RubberyFun/endless-orgasm-machine/doc/building/exhaust_sensor.png

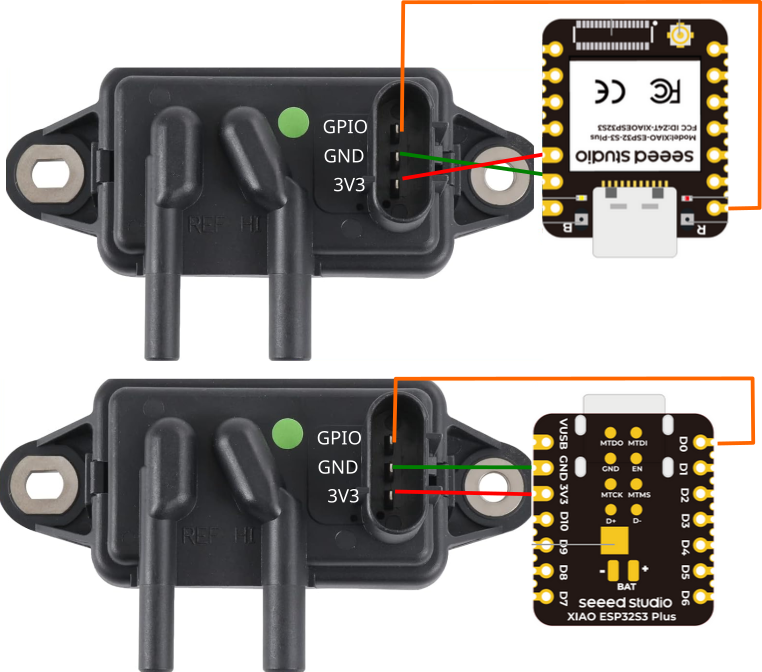
doc/building/exhaust_sensor.png
