RubberyFun/endless-orgasm-machine/doc/building/mprl sensor.png

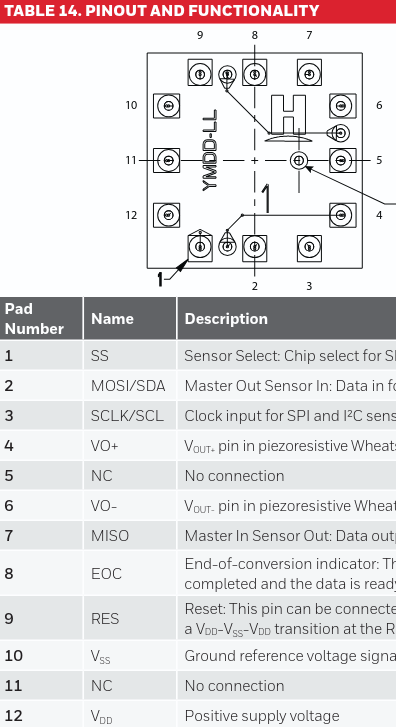
doc/building/mprl sensor.png
