RubberyFun/endless-orgasm-machine/doc/building/mpxv_sensor.png

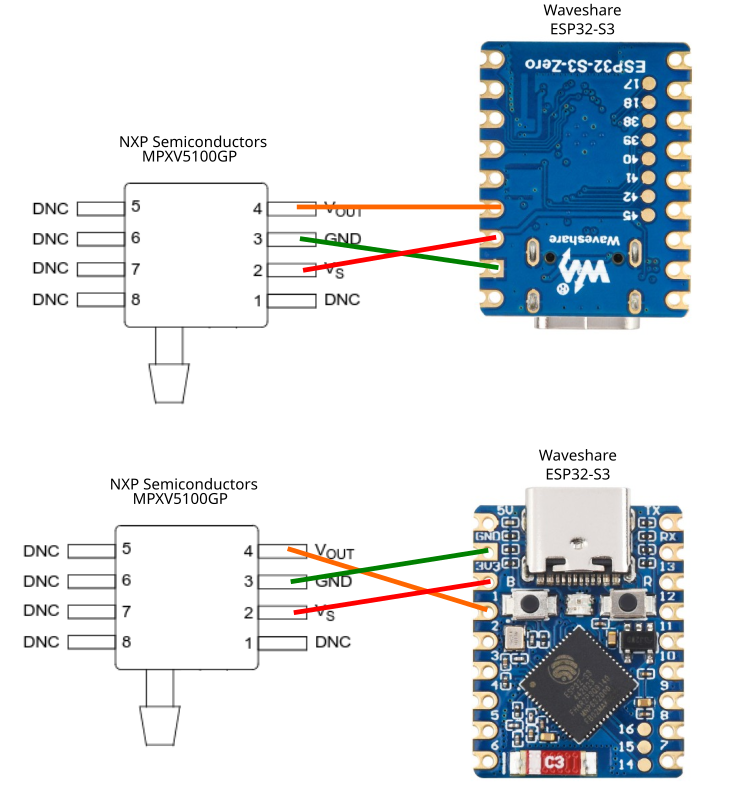
doc/building/mpxv_sensor.png
