RubberyFun/endless-orgasm-machine/doc/building/seed_wiring.png

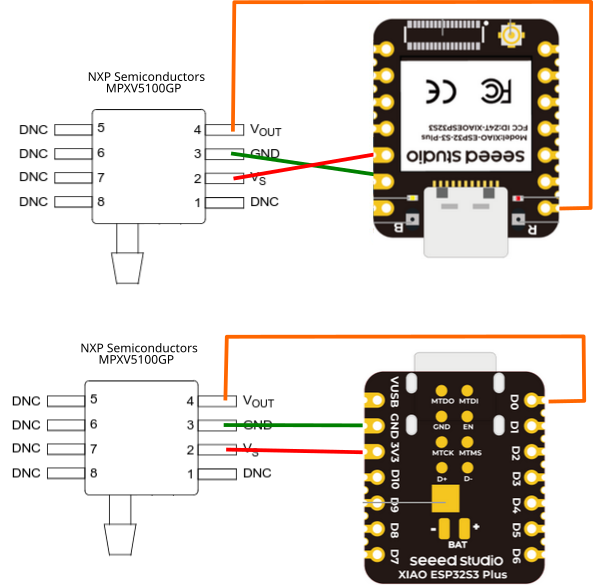
doc/building/seed_wiring.png
