RubberyFun/endless-orgasm-machine/doc/building/Simple analog sensor.png

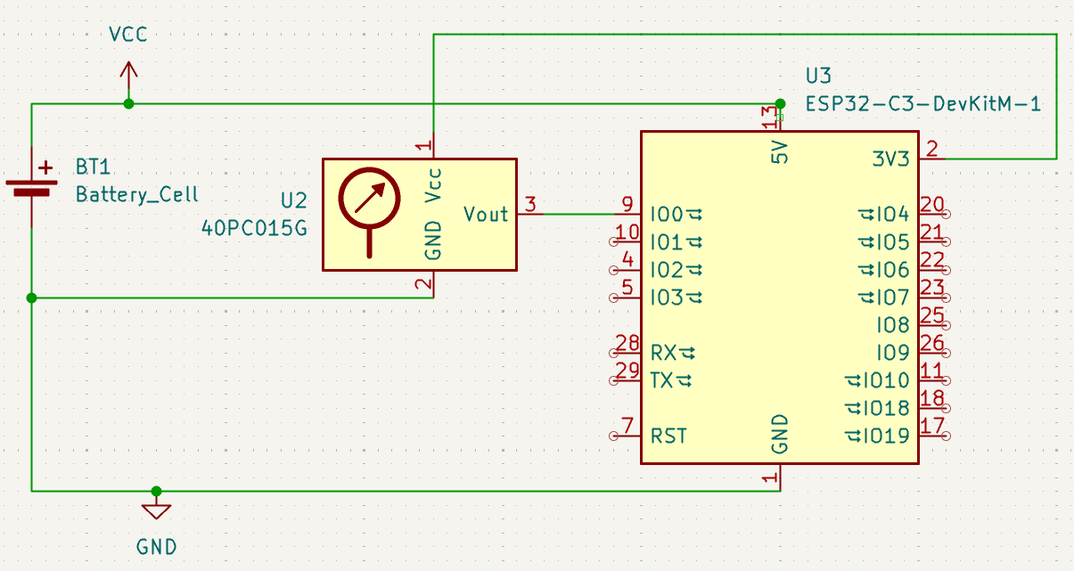
doc/building/Simple analog sensor.png
