RubberyFun/endless-orgasm-machine/src/config_defs.c

#include "config_defs.h"
#include "api/broadcast.h"
#include "config.h"
#include "eom-hal-esp32.h"
#include "esp_err.h"
#include "esp_log.h"
#include "nvs.h"
#include "polyfill.h"
#include <freertos/FreeRTOS.h>
#include <freertos/semphr.h>
#include <stddef.h>
#include <stdio.h>
#include <string.h>
#include <sys/stat.h>
#include <unistd.h>

#define MAX_FILE_PATH_LEN 120

#define NVS_NAMESPACE "config"
#define NVS_LAST_CONFIG_FILE "_filename"

static const char* TAG = "config_defs";

static StaticSemaphore_t sFileMutexStatic;
static SemaphoreHandle_t sFileMutex = NULL;

extern CONFIG_DEFS;

static esp_err_t _store_last_filename(void) {
    esp_err_t err;
    nvs_handle_t nvs;

    err = nvs_open(NVS_NAMESPACE, NVS_READWRITE, &nvs);
    if (err != ESP_OK) goto cleanup;

    err = nvs_set_str(nvs, NVS_LAST_CONFIG_FILE, Config._filename);
    if (err != ESP_OK) goto cleanup;

    err = nvs_commit(nvs);
    if (err != ESP_OK) goto cleanup;

    ESP_LOGI(TAG, "Set last opened filename to: %s\n", Config._filename);
    nvs_close(nvs);
    return ESP_OK;

cleanup:
    ESP_LOGW(TAG, "Trouble storing current config filename: %s\n", esp_err_to_name(err));
    if (nvs) nvs_close(nvs);
    return err;
}

esp_err_t config_init(void) {
    esp_err_t err;
    nvs_handle_t nvs;

    ESP_LOGI(TAG, "Initializing Config access.");

    // Initialize semaphore
    sFileMutex = xSemaphoreCreateMutexStatic(&sFileMutexStatic);

    err = nvs_open(NVS_NAMESPACE, NVS_READONLY, &nvs);
    if (err != ESP_OK) goto defaults;

    size_t len = CONFIG_PATH_MAX;
    err = nvs_get_str(nvs, NVS_LAST_CONFIG_FILE, Config._filename, &len);
    if (err != ESP_OK) goto defaults;

    err = config_load_from_sd(Config._filename, &Config);
    if (err != ESP_OK) goto defaults;

    ESP_LOGI(TAG, "Config loaded from SD: %s\n", Config._filename);

    nvs_close(nvs);

    ESP_LOGI(TAG, "Config initialization complete.");
    return ESP_OK;

defaults:
    if (nvs) nvs_close(nvs);

    if (err == ESP_ERR_NVS_NOT_FOUND || err == ESP_ERR_NOT_FOUND) {
        char path[CONFIG_PATH_MAX + 1] = { 0 };

        //SDHelper_getAbsolutePath(path, CONFIG_PATH_MAX, CONFIG_FILENAME);
        err = config_load_from_sd(CONFIG_FILENAME, &Config);
    }

    if (err != ESP_OK) {
        ESP_LOGW(
            TAG,
            "Trouble loading previous config file, falling back to default: %s\n",
            esp_err_to_name(err)
        );

        config_load_default(&Config);

        if (err == ESP_ERR_INVALID_ARG) {
            //ui_toast("%s", _("Configuration file corrupt. Default values will be used."));
        } else {
            //ui_toast("%s", _("Configuration not found. Default values will be used."));
        }
    }

    return err;
}

// get_config_to_string
void config_serialize(config_t* cfg, char* buf, size_t buflen) {
    cJSON* root = cJSON_CreateObject();
    config_to_json(root, cfg);
    cJSON_PrintPreallocated(root, buf, buflen, true);
    cJSON_Delete(root);
}

// set_config_from_string
esp_err_t config_deserialize(config_t* cfg, const char* buf) {
    esp_err_t err = ESP_OK;
    cJSON* root = cJSON_Parse(buf);
    if (root == NULL) err = ESP_ERR_INVALID_ARG;
    json_to_config(root, cfg);
    cJSON_Delete(root);
    return err;
}

// get_config_to_json
void config_to_json(cJSON* root, config_t* cfg) {
    _config_defs(CFG_GET, root, cfg, NULL, NULL, NULL, 0, NULL);

    // Add version information:
    //cJSON_AddNumberToObject(root, "$version", cfg->_version ? cfg->_version :0);
}

static void _validate_config(config_t* cfg) {
    // Bluetooth and WiFi cannot operate at the same time.
    if (cfg->wifi_on && cfg->bt_on && !cfg->force_bt_coex) {
        ESP_LOGW(TAG, "Not enough memory for WiFi and Bluetooth, disabling BT.");
        cfg->bt_on = false;
    }

    // Update hardware:
    eom_hal_set_sensor_sensitivity(cfg->sensor_sensitivity);
}

static void _migrate_config(cJSON* root) {
    migration_result_t ret = config_system_migrate(root);
    ESP_LOGI(TAG, "Config migrated with status: %d", ret);

    switch (ret) {
    case MIGRATION_COMPLETE:
        config_enqueue_save(1);
        //ui_toast("%s", _("Your config file has updated to work with this version."));
        return;

    case MIGRATION_ERR_TOO_NEW:
        // ui_toast(
        //     "%s",
        //     _("Your config file was created with a newer firmware version and cannot be used.")
        // );
        break;

    case MIGRATION_ERR_BAD_DATA:
        // ui_toast(
        //     "%s", _("There was an error updating your config file to work with this version.")
        // );
        //);
        break;

    default: return;
    }
}

// set_config_from_json
void json_to_config(cJSON* root, config_t* cfg) {
    _migrate_config(root);
    _config_defs(CFG_SET, root, cfg, NULL, NULL, NULL, 0, NULL);
    _validate_config(cfg);

    cJSON* root_version = cJSON_GetObjectItem(root, "$version");
    if (root_version != NULL) cfg->_version = root_version->valueint;
}

// merge_config_from_json
void json_to_config_merge(cJSON* root, config_t* cfg) {
    _migrate_config(root);
    _config_defs(CFG_MERGE, root, cfg, NULL, NULL, NULL, 0, NULL);
    _validate_config(cfg);
}

bool set_config_value(const char* option, const char* value, bool* require_reboot) {
    if (_config_defs(CFG_SET, NULL, &Config, option, value, NULL, 0, require_reboot)) {
        _validate_config(&Config);
        return true;
    }

    return false;
}

bool get_config_value(const char* option, char* buffer, size_t len) {
    if (_config_defs(CFG_GET, NULL, &Config, option, NULL, buffer, len, NULL)) {
        return true;
    }

    return false;
}

/**
 * @brief Enqueue a save after a particular delay. To check or tick, pass -1 for arg.
 *
 * @param delay Delay in MS after which to save, to prevent repeated duplicates. 0 to save now, -1
 * to tick.
 */
void config_enqueue_save(long delay) {
    static unsigned long save_at_ms_tick = 0;
    unsigned long millis = esp_timer_get_time() / 1000UL;

    if (delay > 0) {
        // Queue a future save:
        save_at_ms_tick = millis + delay;
    } else {
        if (delay == 0 || (save_at_ms_tick > 0 && save_at_ms_tick < millis)) {
            if (Config._filename[0] == '\0') {
                ESP_LOGW(TAG, "Attempt to save config without a _filename!");
                save_at_ms_tick = 0;
                return;
            }

            ESP_LOGI(
                TAG,
                "Saving now from future save queue... (delay=%ld, at=%ld, ms=%ld)",
                delay,
                save_at_ms_tick,
                millis
            );

            config_save_to_sd(Config._filename, &Config);
            api_broadcast_config();
            save_at_ms_tick = 0;
        }
    }
}

/**
 * Cast a string to a bool. Accepts "false", "no", "off", "0" to false, all other
 * strings cast to true.
 * @param a
 * @return
 */
bool atob(const char* a) {
    return !(
        strcasecmp(a, "false") == 0 || strcasecmp(a, "no") == 0 || strcasecmp(a, "off") == 0 ||
        strcasecmp(a, "0") == 0
    );
}

// Here There Be Dragons Indeed

esp_err_t config_load_from_sd(const char* path, config_t* cfg) {
    esp_err_t err = ESP_OK;
    FILE* f = NULL;
    long fsize;
    char* buffer = NULL;
    size_t result;

    if (!xSemaphoreTake(sFileMutex, portMAX_DELAY)) {
        ESP_LOGW(TAG, "Failed to take file lock for config load.");
        err = ESP_ERR_TIMEOUT;
        goto cleanup;
    }

    f = fopen(path, "r");

    // Sometimes the first file read fails:
    if (!f) {
        f = fopen(path, "r");
    }

    if (!f) {
        ESP_LOGW(TAG, "File does not exist: %s", path);
        err = ESP_ERR_NOT_FOUND;
        goto cleanup;
    }

    if (f == NULL) {
        ESP_LOGE(TAG, "Failed to open file for reading: %s", path);
        err = ESP_FAIL;
        goto cleanup;
    }

    fseek(f, 0, SEEK_END);
    fsize = ftell(f);
    rewind(f);

    ESP_LOGD(TAG, "Allocating %ld bytes for file: %s", fsize, path);
    buffer = (char*)malloc(fsize + 1);

    if (!buffer) {
        ESP_LOGE(TAG, "Failed to allocate memory for file: %s", path);
        err = ESP_FAIL;
        goto cleanup;
    }

    result = fread(buffer, 1, fsize, f);
    buffer[fsize] = '\0';

    if (result != fsize) {
        ESP_LOGE(TAG, "Failed to read file: %s", path);
        err = ESP_FAIL;
        goto cleanup;
    }

    ESP_LOGI(TAG, "Loaded %ld bytes from %s\n%s", fsize, path, buffer);

    err = config_deserialize(cfg, buffer);
    if (err != ESP_OK) {
        ESP_LOGE(TAG, "Error deserializing config file.");
        goto cleanup;
    }

    // Update config path:
    strlcpy(cfg->_filename, path, CONFIG_PATH_MAX);

    if (&Config == cfg) {
        _store_last_filename();
    }

cleanup:
    if (f) fclose(f);
    if (buffer) free(buffer);
    xSemaphoreGive(sFileMutex);

    return err;
}

esp_err_t config_save_to_sd(const char* path, config_t* cfg) {
    //if (eom_hal_get_sd_size_bytes() <= 0) {
        // ESP_LOGW(TAG, "Request to save to SD without SD present.");
        // return ESP_ERR_NO_MEM;
    //}

    if (!xSemaphoreTake(sFileMutex, portMAX_DELAY)) {
        ESP_LOGW(TAG, "Failed to take file lock for config save.");
        return ESP_ERR_TIMEOUT;
    }

    cJSON* root = cJSON_CreateObject();
    struct stat st;

    config_to_json(root, cfg);

    // Delete old config if it exists:
    if (stat(path, &st) == 0) {
        char bak_path[MAX_FILE_PATH_LEN + 1] = "";
        strlcpy(bak_path, path, MAX_FILE_PATH_LEN);
        strlcat(bak_path, ".bak", MAX_FILE_PATH_LEN);

        unlink(bak_path);

        if (rename(path, bak_path) != 0) {
            ESP_LOGE(TAG, "Failed to rename %s to %s", path, bak_path);
            xSemaphoreGive(sFileMutex);
            return ESP_FAIL;
        }
    }

    FILE* f = fopen(path, "w");

    if (f == NULL) {
        ESP_LOGE(TAG, "Failed to open file for writing: %s", path);
        xSemaphoreGive(sFileMutex);
        return ESP_FAIL;
    }

    char* json = cJSON_Print(root);
    fputs(json, f);
    long fsize = ftell(f);
    fclose(f);

    ESP_LOGD(TAG, "Wrote %ld bytes:\n%s", fsize, json);

    // Update config path:
    if (strcmp(path, cfg->_filename)) {
        strlcpy(cfg->_filename, path, CONFIG_PATH_MAX);

        // Update our last active config file:
        if (&Config == cfg) {
            _store_last_filename();
        }
    }

    cJSON_Delete(root);
    cJSON_free(json);
    xSemaphoreGive(sFileMutex);

    return ESP_OK;
}


void config_load_default(config_t* cfg) {
    ESP_LOGI(TAG, "Loading default config...");
    cJSON* root = cJSON_CreateObject();
    cJSON_AddNumberToObject(root, "$version", SYSTEM_CONFIG_FILE_VERSION);
    json_to_config(root, cfg);
    strcpy(cfg->_filename, CONFIG_FILENAME);
    cJSON_Delete(root);
}
